Charliegroup/ProjetoPI/Projeto_Integrador_Grupo_Charlie/Documentos/Ferramenta_Antiga/Explicacao.png

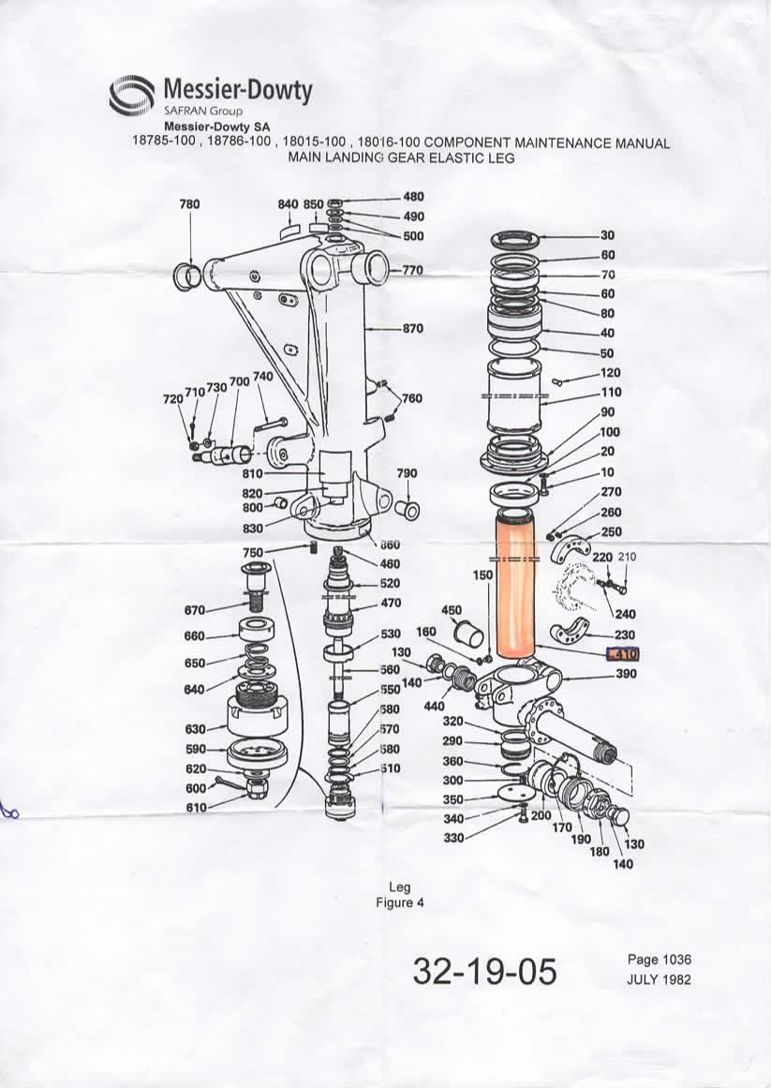
Projeto_Integrador_Grupo_Charlie/Documentos/Ferramenta_Antiga/Explicacao.png
