Charliegroup/ProjetoPI/Projeto_Integrador_Grupo_Charlie/Imagens/Croqui_a_mao/Ferramenta_Croqui_a_mao.png

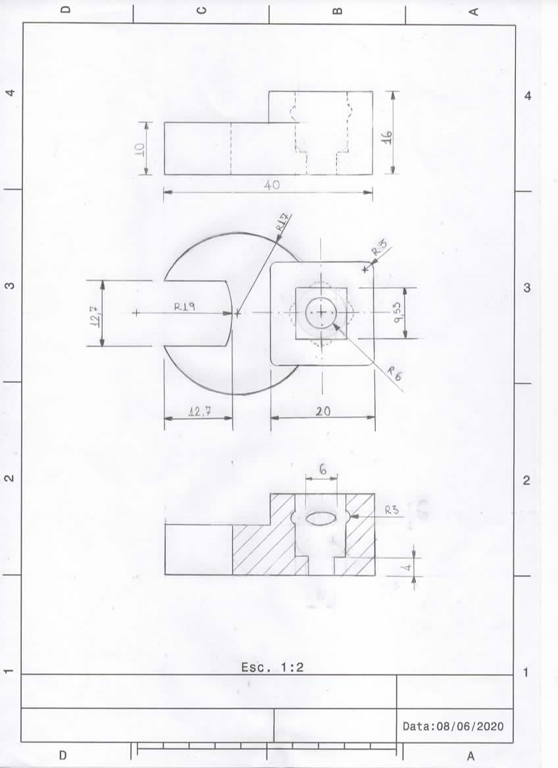
Projeto_Integrador_Grupo_Charlie/Imagens/Croqui_a_mao/Ferramenta_Croqui_a_mao.png
