Charliegroup/ProjetoPI/Projeto_Integrador_Grupo_Charlie/Imagens/Ferramenta_Exemplo/Ferramenta_Exemplo3.jpg

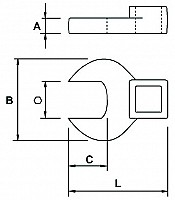
Projeto_Integrador_Grupo_Charlie/Imagens/Ferramenta_Exemplo/Ferramenta_Exemplo3.jpg
