Charliegroup/ProjetoPI/Projeto_Integrador_Grupo_Charlie/Imagens/Ferramenta_Exemplo/Ferramenta_Exemplo.jpg

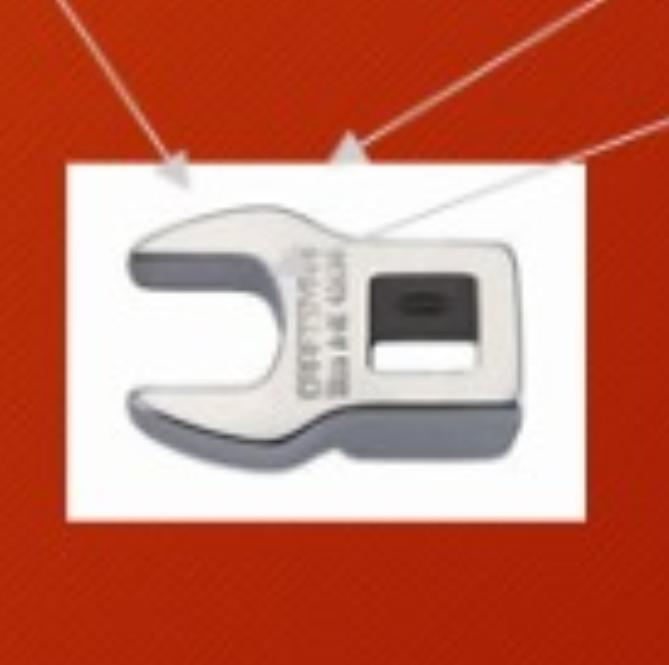
Projeto_Integrador_Grupo_Charlie/Imagens/Ferramenta_Exemplo/Ferramenta_Exemplo.jpg
