Charliegroup/ProjetoPI/Projeto_Integrador_Grupo_Charlie/Imagens/Ferramenta_Exemplo/images.jpg

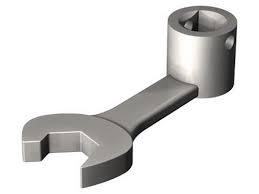
Projeto_Integrador_Grupo_Charlie/Imagens/Ferramenta_Exemplo/images.jpg
