Charliegroup/ProjetoPI/Projeto_Integrador_Grupo_Charlie/Imagens/Imagens_README/Utilizacao_README.png

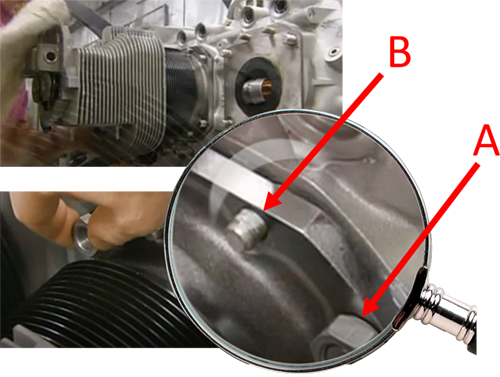
Projeto_Integrador_Grupo_Charlie/Imagens/Imagens_README/Utilizacao_README.png
