Charliegroup/ProjetoPI/Projeto_Integrador_Grupo_Charlie/Imagens/Imagens_README/UtilizacaoREADME_2.png

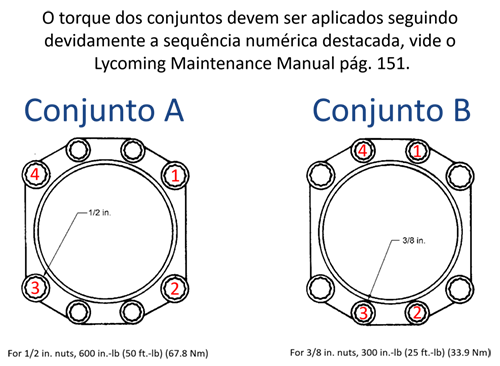
Projeto_Integrador_Grupo_Charlie/Imagens/Imagens_README/UtilizacaoREADME_2.png
