Charliegroup/ProjetoPI/Projeto_Integrador_Grupo_Charlie/Imagens/Perspectivas/Perspectiva A.png

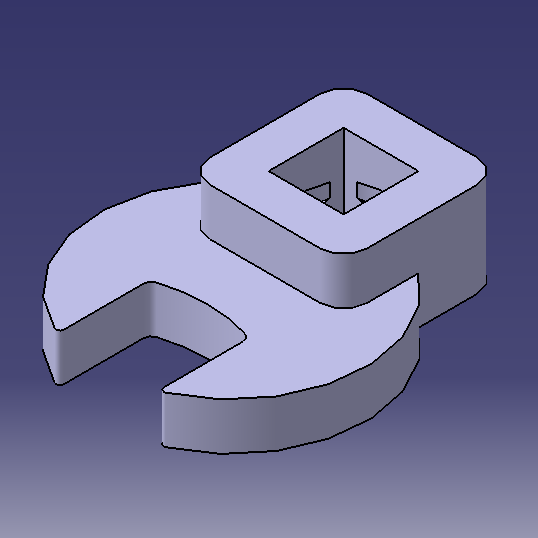
Projeto_Integrador_Grupo_Charlie/Imagens/Perspectivas/Perspectiva A.png
