Charliegroup/ProjetoPI/Projeto_Integrador_Grupo_Charlie/Imagens/Perspectivas/Perspectiva_B.png

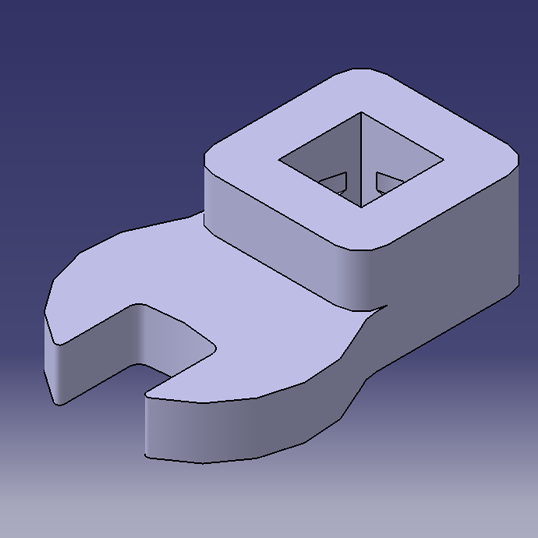
Projeto_Integrador_Grupo_Charlie/Imagens/Perspectivas/Perspectiva_B.png
