Charliegroup/ProjetoPI/Projeto_Integrador_Grupo_Charlie/Imagens/Planejamento_EAP/EAP_Grupo_Charlie_Projeto.png

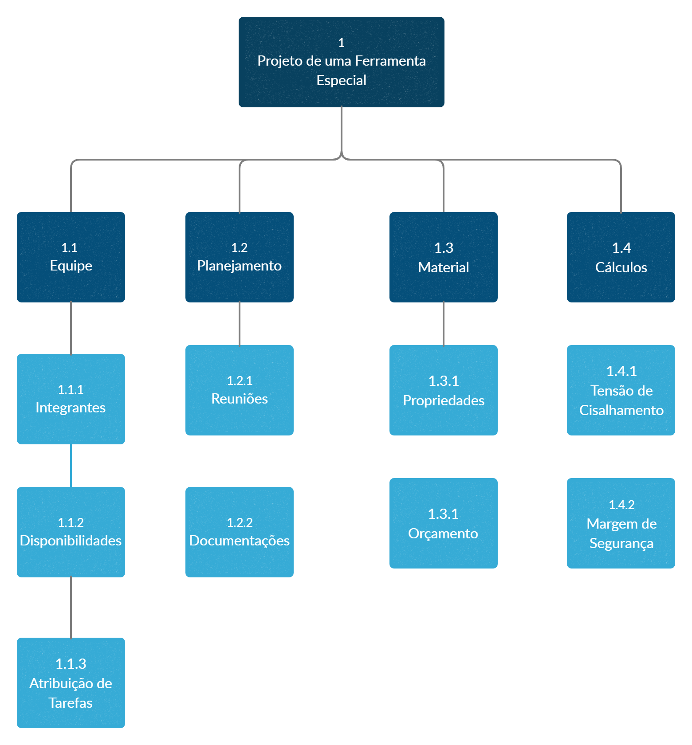
Projeto_Integrador_Grupo_Charlie/Imagens/Planejamento_EAP/EAP_Grupo_Charlie_Projeto.png
