Charliegroup/ProjetoPI/Projeto_Integrador_Grupo_Charlie/Imagens/Templates_Power_Point/Aco_Cromo_Vanadio_Exemplo.png

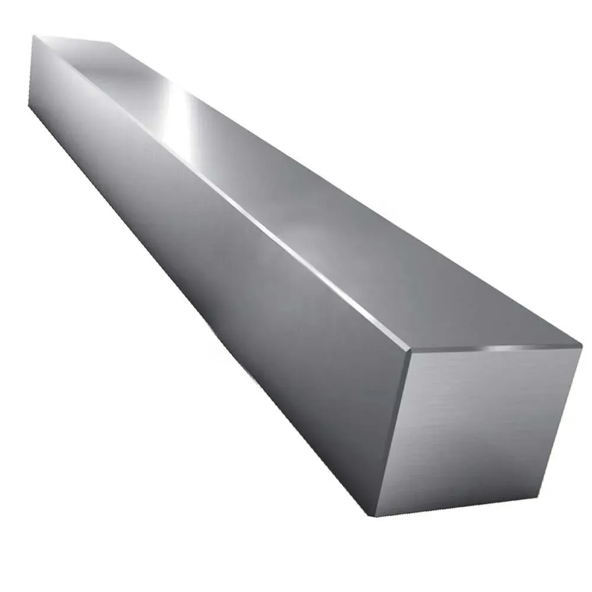
Projeto_Integrador_Grupo_Charlie/Imagens/Templates_Power_Point/Aco_Cromo_Vanadio_Exemplo.png
