Charliegroup/ProjetoPI/Projeto_Integrador_Grupo_Charlie/Imagens/Templates_Power_Point/Capa PI-PP.png

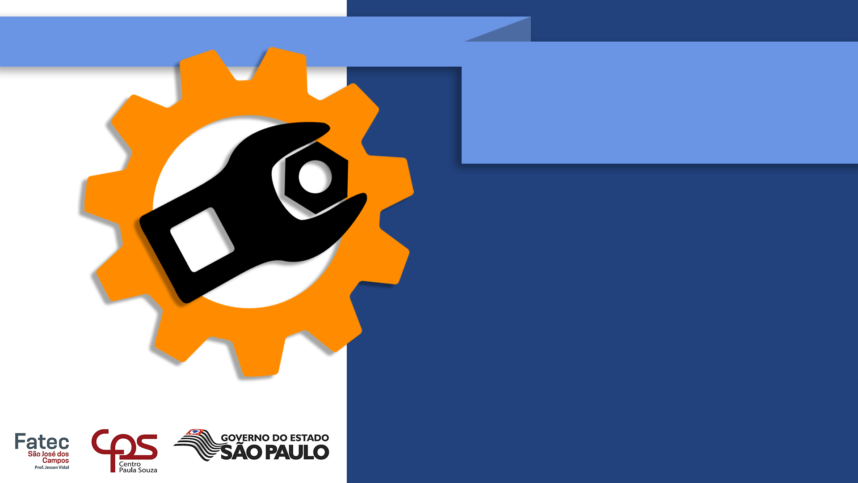
Projeto_Integrador_Grupo_Charlie/Imagens/Templates_Power_Point/Capa PI-PP.png
