Charliegroup/ProjetoPI/Projeto_Integrador_Grupo_Charlie/Imagens/Templates_Power_Point/Chave_A_Especificações.png

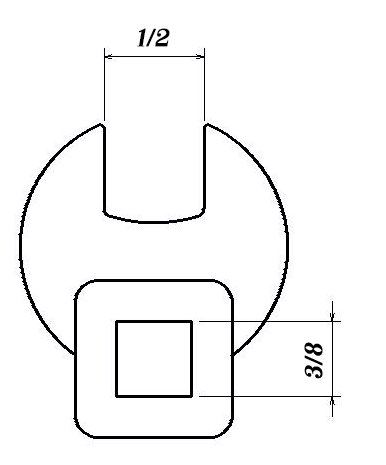
Projeto_Integrador_Grupo_Charlie/Imagens/Templates_Power_Point/Chave_A_Especificações.png
