Charliegroup/ProjetoPI/Projeto_Integrador_Grupo_Charlie/Imagens/Templates_Power_Point/Chave_B_Especificacoes.png

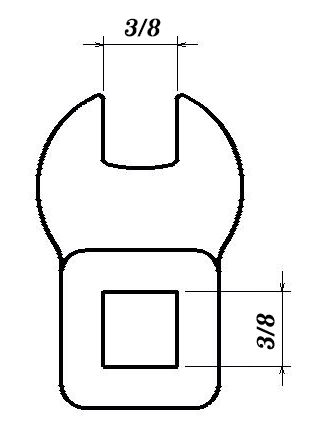
Projeto_Integrador_Grupo_Charlie/Imagens/Templates_Power_Point/Chave_B_Especificacoes.png
