Charliegroup/ProjetoPI/Projeto_Integrador_Grupo_Charlie/Imagens/Templates_Power_Point/Cisalhamento_B.png

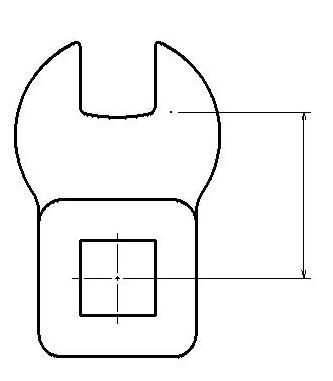
Projeto_Integrador_Grupo_Charlie/Imagens/Templates_Power_Point/Cisalhamento_B.png
