Charliegroup/ProjetoPI/Projeto_Integrador_Grupo_Charlie/Imagens/Templates_Power_Point/Conjunto_A.png

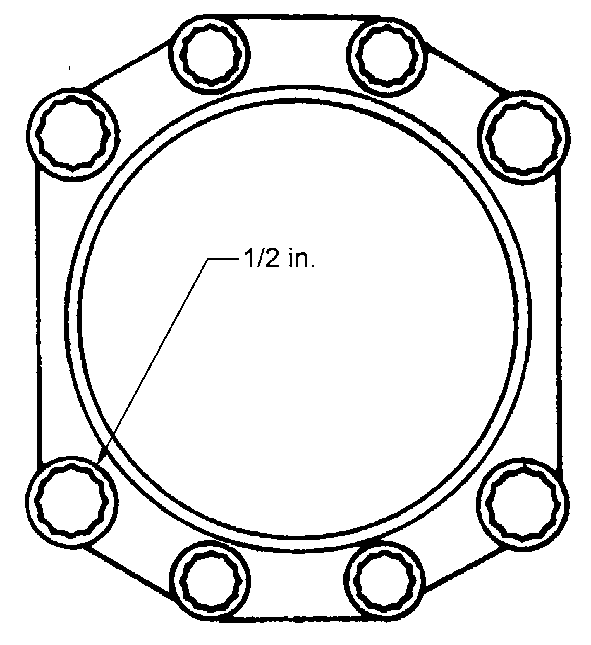
Projeto_Integrador_Grupo_Charlie/Imagens/Templates_Power_Point/Conjunto_A.png
