Charliegroup/ProjetoPI/Projeto_Integrador_Grupo_Charlie/Imagens/Templates_Power_Point/Ferramenta proposta.png

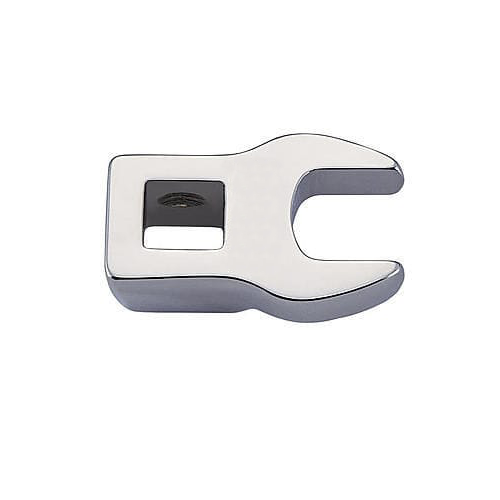
Projeto_Integrador_Grupo_Charlie/Imagens/Templates_Power_Point/Ferramenta proposta.png
