Charliegroup/ProjetoPI/Projeto_Integrador_Grupo_Charlie/Imagens/Templates_Power_Point/image--002.png

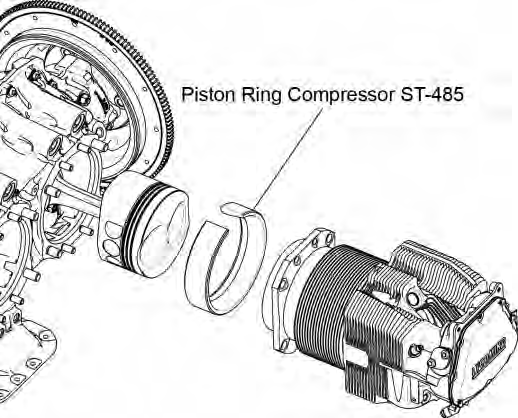
Projeto_Integrador_Grupo_Charlie/Imagens/Templates_Power_Point/image--002.png
