Charliegroup/ProjetoPI/Projeto_Integrador_Grupo_Charlie/Imagens/Templates_Power_Point/Lupa.png

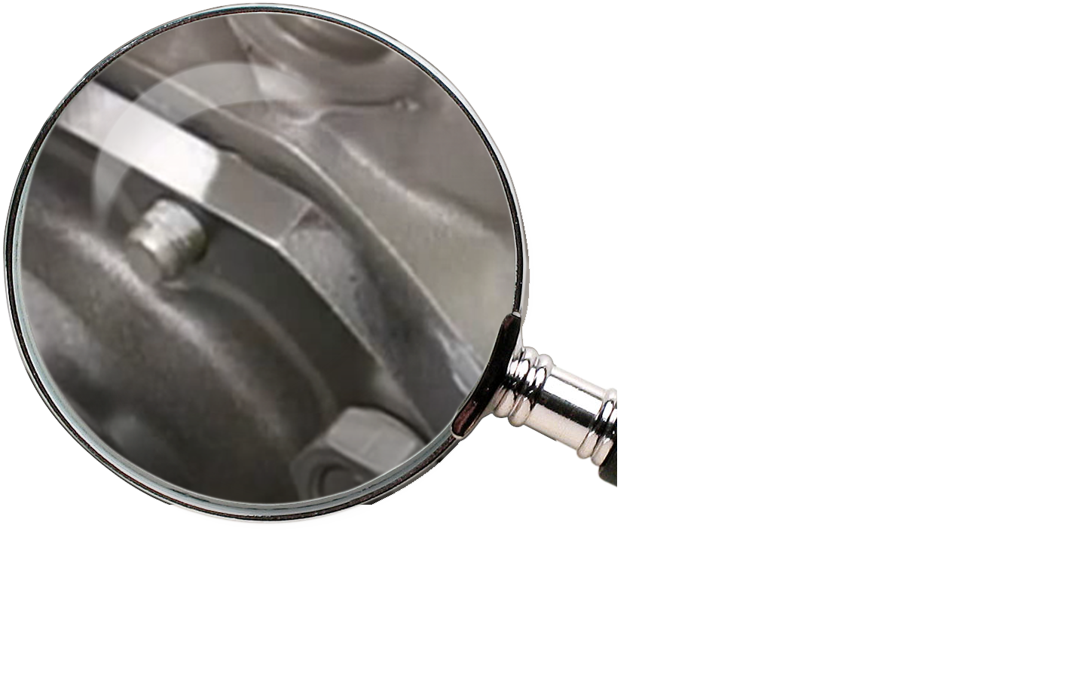
Projeto_Integrador_Grupo_Charlie/Imagens/Templates_Power_Point/Lupa.png
