Charliegroup/ProjetoPI/Projeto_Integrador_Grupo_Charlie/Imagens/Templates_Power_Point/PI_Diagrama.png

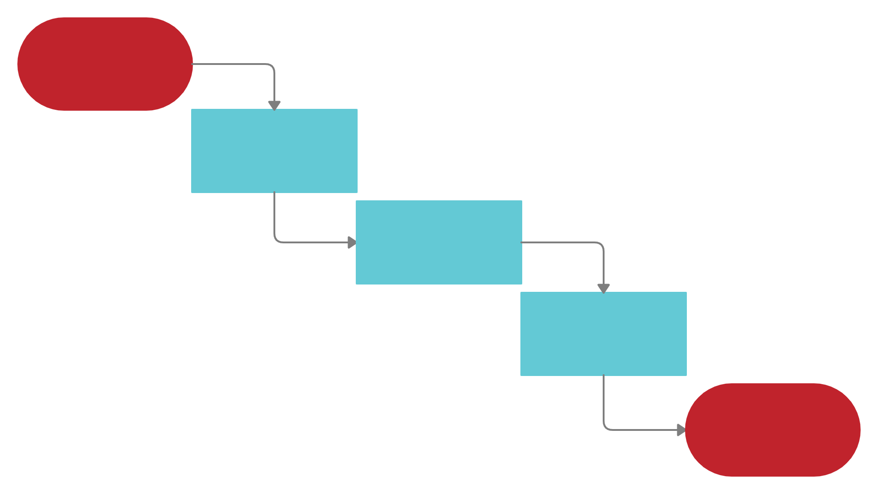
Projeto_Integrador_Grupo_Charlie/Imagens/Templates_Power_Point/PI_Diagrama.png
