Charliegroup/ProjetoPI/Projeto_Integrador_Grupo_Charlie/Imagens/Templates_Power_Point/template 1.png

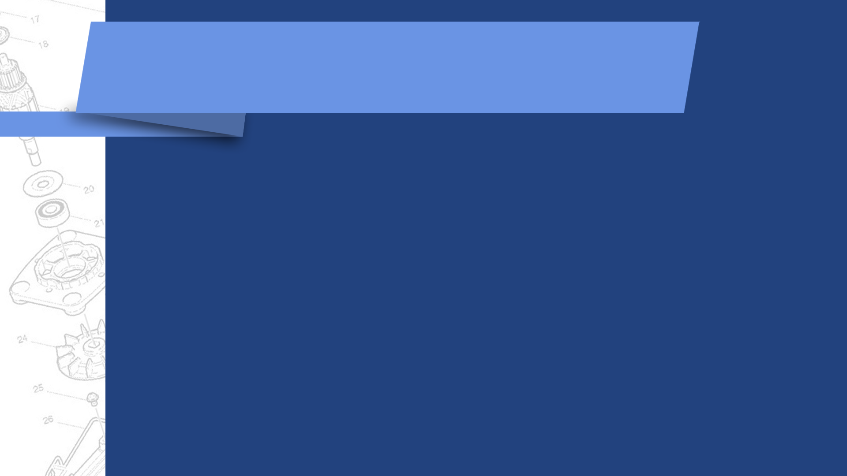
Projeto_Integrador_Grupo_Charlie/Imagens/Templates_Power_Point/template 1.png
