Charliegroup/ProjetoPI/Projeto_Integrador_Grupo_Charlie/Imagens/Templates_Power_Point/template 2.png

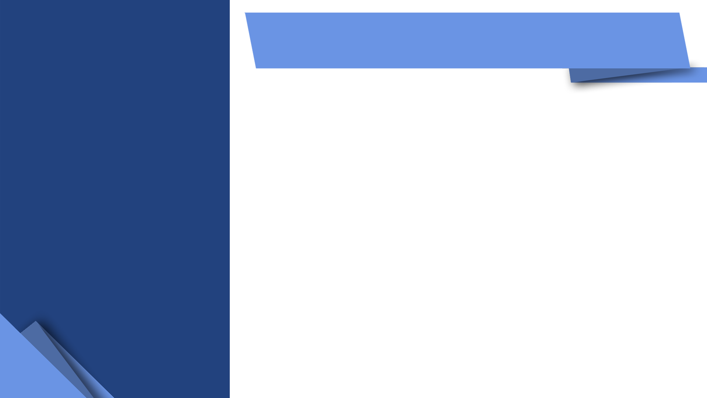
Projeto_Integrador_Grupo_Charlie/Imagens/Templates_Power_Point/template 2.png
