Charliegroup/ProjetoPI/Projeto_Integrador_Grupo_Charlie/Imagens/Templates_Power_Point/Torquimetro/51m8QTj8xkL._AC_SL1200_.jpg

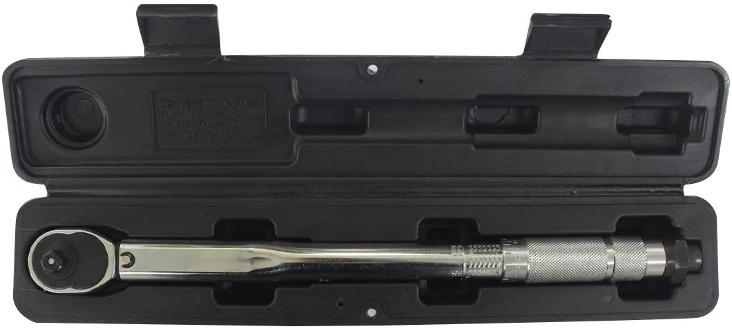
Projeto_Integrador_Grupo_Charlie/Imagens/Templates_Power_Point/Torquimetro/51m8QTj8xkL._AC_SL1200_.jpg
