Charliegroup/ProjetoPI/Projeto_Integrador_Grupo_Charlie/Imagens/Templates_Power_Point/Torquimetro/519om+6jGuL._AC_SL1200_.jpg

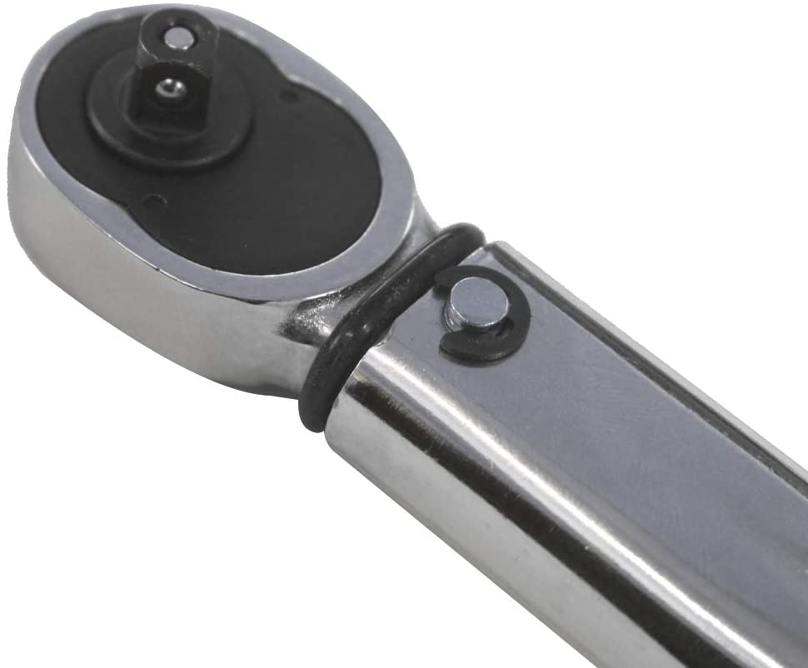
Projeto_Integrador_Grupo_Charlie/Imagens/Templates_Power_Point/Torquimetro/519om+6jGuL._AC_SL1200_.jpg
