Charliegroup/ProjetoPI/Projeto_Integrador_Grupo_Charlie/CAD/Drawing/Drawing_Teste/Drawing_2D/Drawing1_Chave_PI.jpg

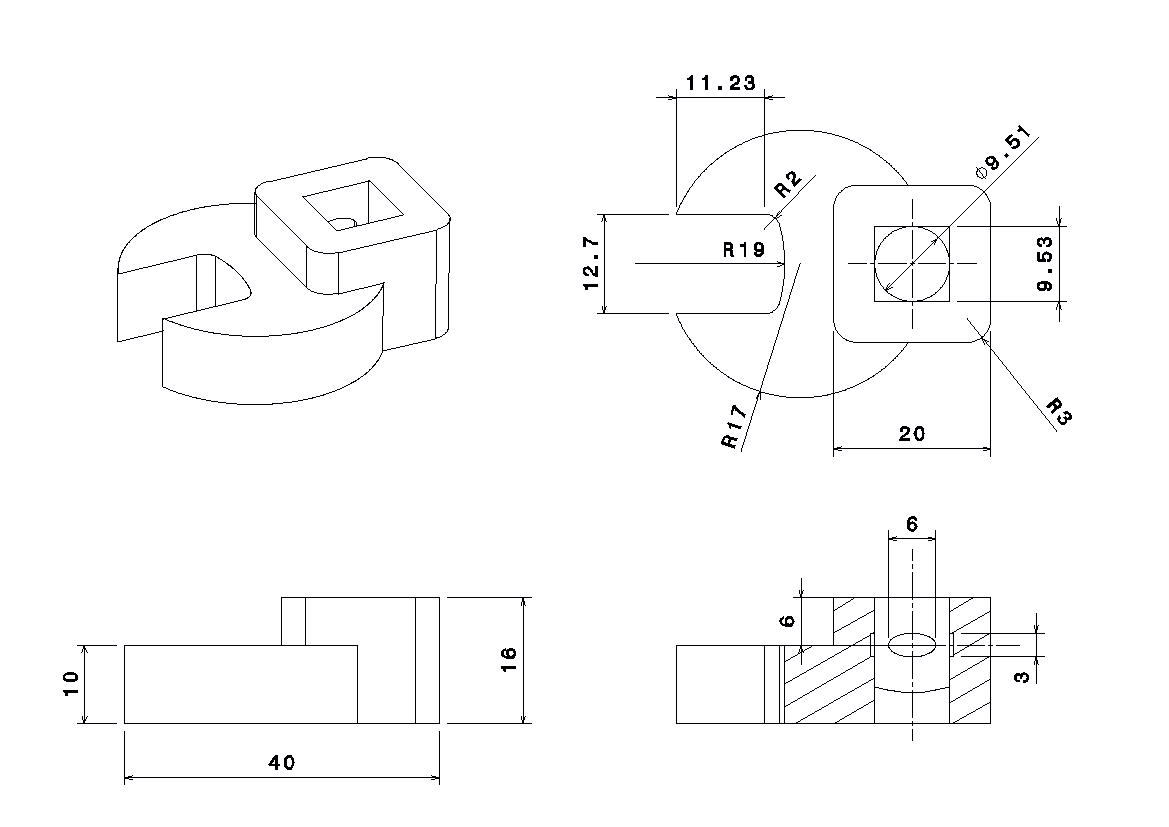
Projeto_Integrador_Grupo_Charlie/CAD/Drawing/Drawing_Teste/Drawing_2D/Drawing1_Chave_PI.jpg
