Charliegroup/ProjetoPI/Projeto_Integrador_Grupo_Charlie/Imagens/Templates_Power_Point/Torquimetro/41dv4e1qa3L._AC_SL1200_.jpg

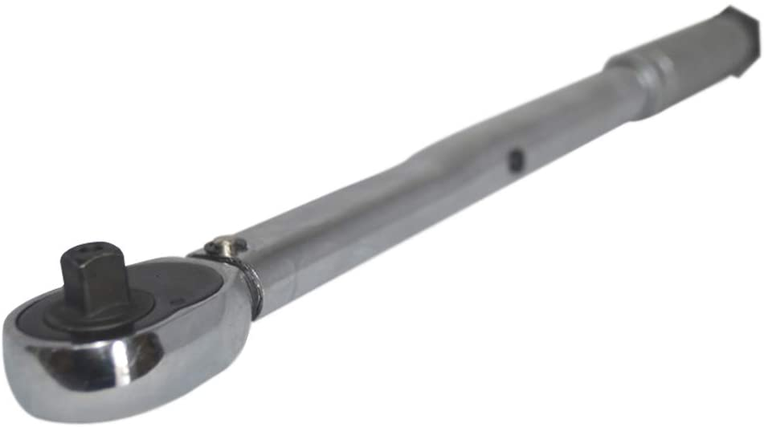
Projeto_Integrador_Grupo_Charlie/Imagens/Templates_Power_Point/Torquimetro/41dv4e1qa3L._AC_SL1200_.jpg
